anishmalladi05/Touch-ID/PCB/TouchID.kicad_sch

## KiCad design PCB/TouchID.kicad_sch (2026-08-20)

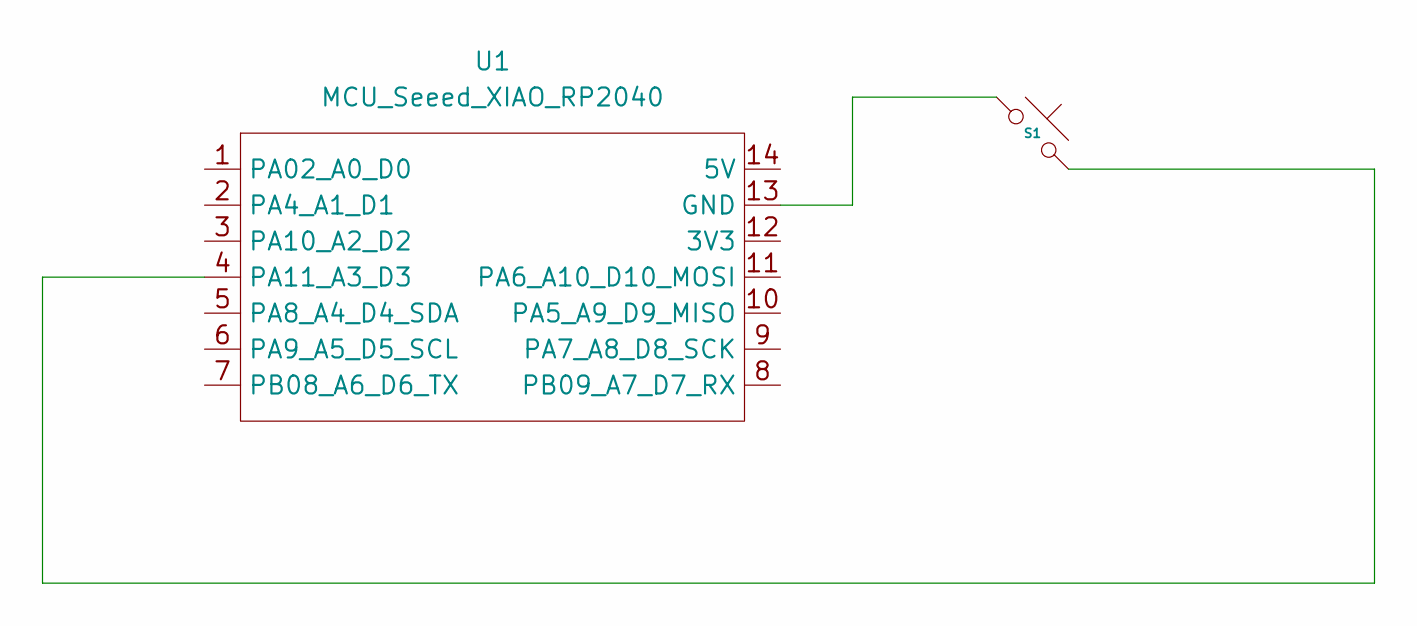
[picture p4: schematic TouchID.kicad_sch]

Parts:
S1: MX_PCB_1.00u
U1: MCU_Seeed_XIAO_RP2040; Seeed_XIAO_RP2040

Connections:
unnamed: S1.1, U1.13 (GND)
unnamed: S1.2, U1.4 (PA11_A3_D3)
